93857536-pixel/saoti-guajian/firmware/data/test_question.jpg

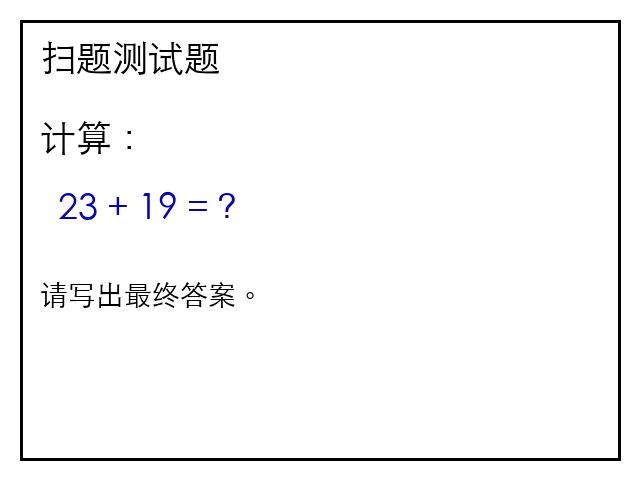
firmware/data/test_question.jpg
