93857536-pixel/saoti-guajian/firmware/include/test_question_jpeg.h

#pragma once
#include <stddef.h>
#include <stdint.h>

// Embedded fixed question image for camera-bypass AI test (23+19=?).
// Source: data/test_question.jpg (21733 bytes)
static const uint8_t kTestQuestionJpeg[] = {
  0xff, 0xd8, 0xff, 0xe0, 0x00, 0x10, 0x4a, 0x46, 0x49, 0x46, 0x00, 0x01, 0x01, 0x00, 0x00, 0x01,
  0x00, 0x01, 0x00, 0x00, 0xff, 0xdb, 0x00, 0x43, 0x00, 0x05, 0x03, 0x04, 0x04, 0x04, 0x03, 0x05,
  0x04, 0x04, 0x04, 0x05, 0x05, 0x05, 0x06, 0x07, 0x0c, 0x08, 0x07, 0x07, 0x07, 0x07, 0x0f, 0x0b,
  0x0b, 0x09, 0x0c, 0x11, 0x0f, 0x12, 0x12, 0x11, 0x0f, 0x11, 0x11, 0x13, 0x16, 0x1c, 0x17, 0x13,
  0x14, 0x1a, 0x15, 0x11, 0x11, 0x18, 0x21, 0x18, 0x1a, 0x1d, 0x1d, 0x1f, 0x1f, 0x1f, 0x13, 0x17,
  0x22, 0x24, 0x22, 0x1e, 0x24, 0x1c, 0x1e, 0x1f, 0x1e, 0xff, 0xdb, 0x00, 0x43, 0x01, 0x05, 0x05,
  0x05, 0x07, 0x06, 0x07, 0x0e, 0x08, 0x08, 0x0e, 0x1e, 0x14, 0x11, 0x14, 0x1e, 0x1e, 0x1e, 0x1e,
  0x1e, 0x1e, 0x1e, 0x1e, 0x1e, 0x1e, 0x1e, 0x1e, 0x1e, 0x1e, 0x1e, 0x1e, 0x1e, 0x1e, 0x1e, 0x1e,
  0x1e, 0x1e, 0x1e, 0x1e, 0x1e, 0x1e, 0x1e, 0x1e, 0x1e, 0x1e, 0x1e, 0x1e, 0x1e, 0x1e, 0x1e, 0x1e,
  0x1e, 0x1e, 0x1e, 0x1e, 0x1e, 0x1e, 0x1e, 0x1e, 0x1e, 0x1e, 0x1e, 0x1e, 0x1e, 0x1e, 0xff, 0xc0,
  0x00, 0x11, 0x08, 0x01, 0xe0, 0x02, 0x80, 0x03, 0x01, 0x22, 0x00, 0x02, 0x11, 0x01, 0x03, 0x11,
  0x01, 0xff, 0xc4, 0x00, 0x1f, 0x00, 0x00, 0x01, 0x05, 0x01, 0x01, 0x01, 0x01, 0x01, 0x01, 0x00,
  0x00, 0x00, 0x00, 0x00, 0x00, 0x00, 0x00, 0x01, 0x02, 0x03, 0x04, 0x05, 0x06, 0x07, 0x08, 0x09,
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
  0xfa, 0xff, 0xda, 0x00, 0x0c, 0x03, 0x01, 0x00, 0x02, 0x11, 0x03, 0x11, 0x00, 0x3f, 0x00, 0xfb,
  0x2e, 0x8a, 0x28, 0xa0, 0x02, 0x8a, 0x28, 0xa0, 0x02, 0x8a, 0x28, 0xa0, 0x02, 0x8a, 0x28, 0xa0,
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
};
static const size_t kTestQuestionJpegLen = sizeof(kTestQuestionJpeg);
